jarviscog/Bertha3/CAD Files/parts/frontv2.SLDPRT

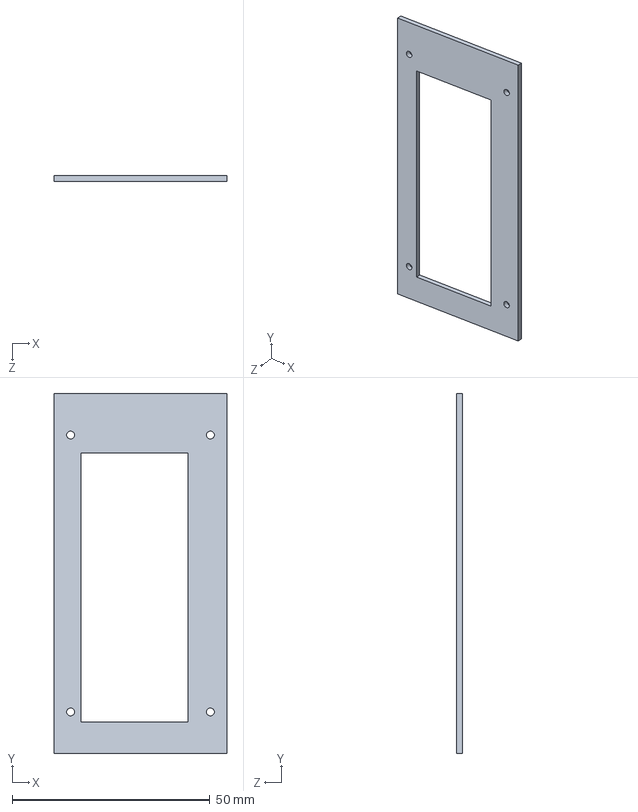
[picture p15: CAD file, 2022-08-08]
CAD Files/parts/frontv2.SLDPRT
43.7 x 91.0 x 1.50 mm
