jarviscog/Bertha3/Parts/EndCap.SLDPRT

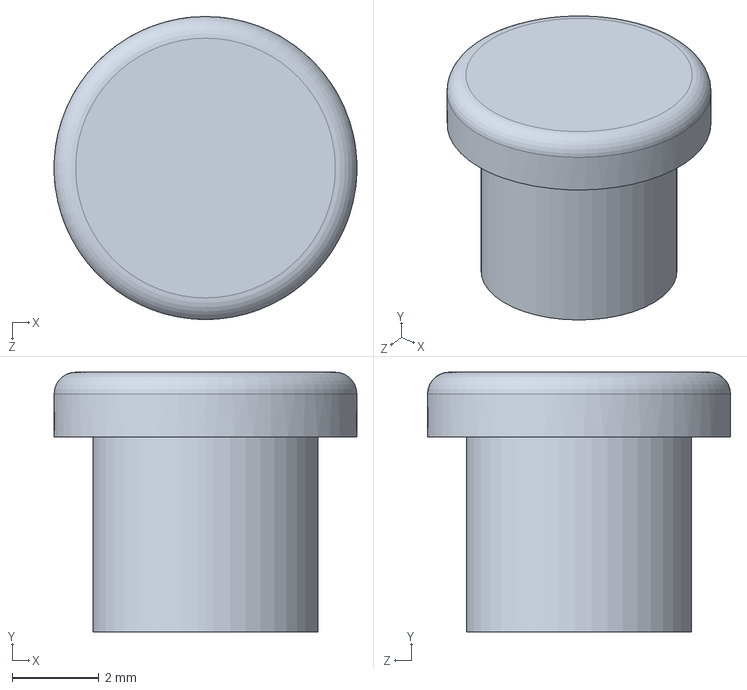
[picture p16: CAD file, 2021-05-19]
Parts/EndCap.SLDPRT
7.00 x 6.00 x 7.00 mm
