jarviscog/Bertha3/CAD Files/parts/fasteners.SLDPRT

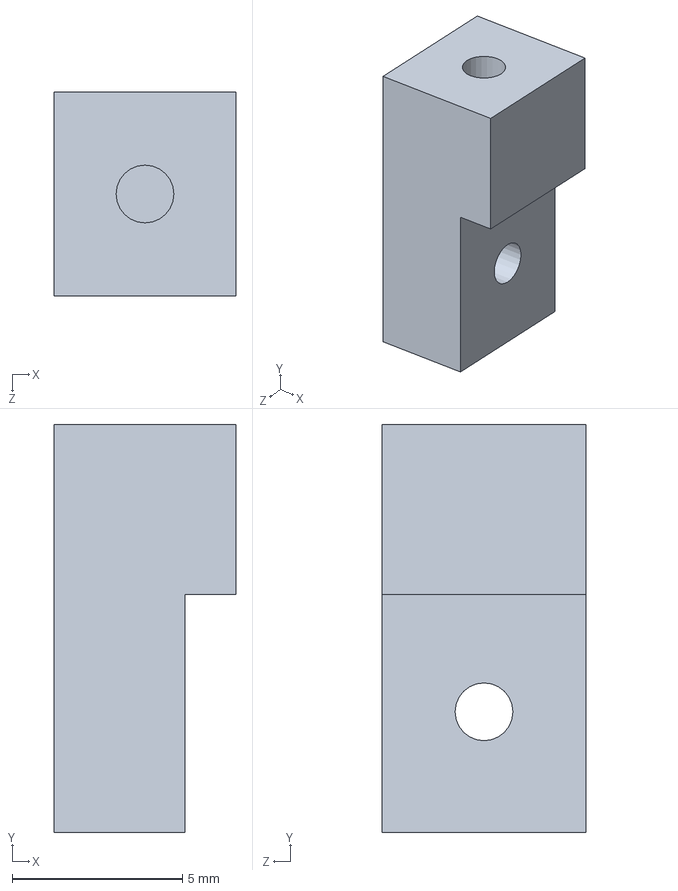
[picture p17: CAD file, 2022-08-08]
CAD Files/parts/fasteners.SLDPRT
5.35 x 12.0 x 6.00 mm
