jarviscog/Bertha3/Parts/SinisterGear.SLDPRT

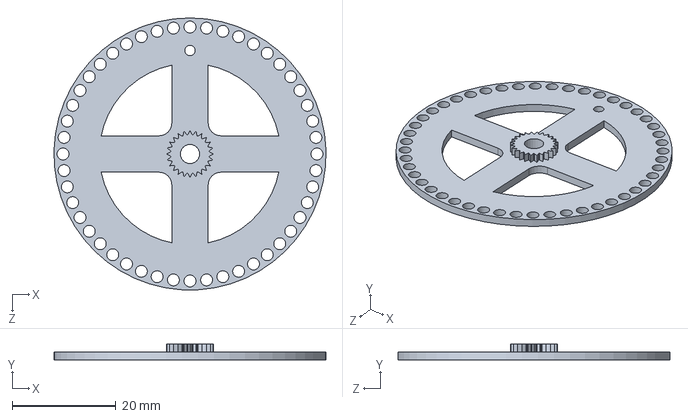
[picture p18: CAD file, 2021-05-19]
Parts/SinisterGear.SLDPRT
52.5 x 3.00 x 52.5 mm
