jarviscog/Bertha3/CAD Files/parts/Right.SLDPRT

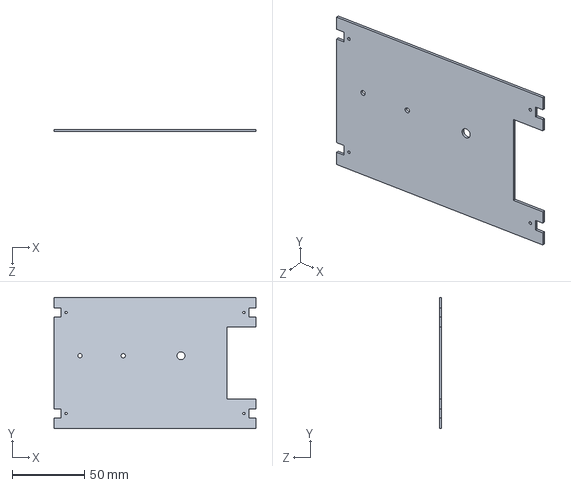
[picture p19: CAD file, 2022-08-08]
CAD Files/parts/Right.SLDPRT
140.0 x 91.0 x 1.50 mm
