jarviscog/Bertha3/Parts/Metal Rod.SLDPRT

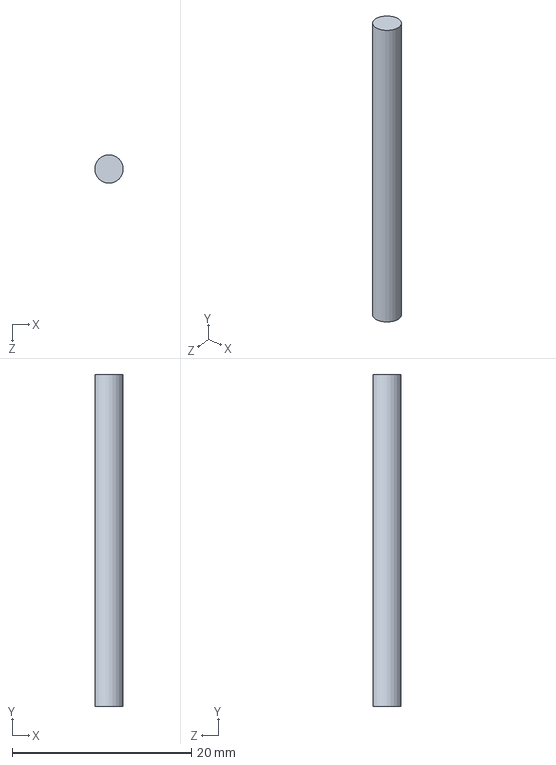
[picture p20: CAD file, 2021-05-19]
Parts/Metal Rod.SLDPRT
3.17 x 37.0 x 3.17 mm
