jarviscog/Bertha3/CAD Files/parts/backplate.SLDPRT

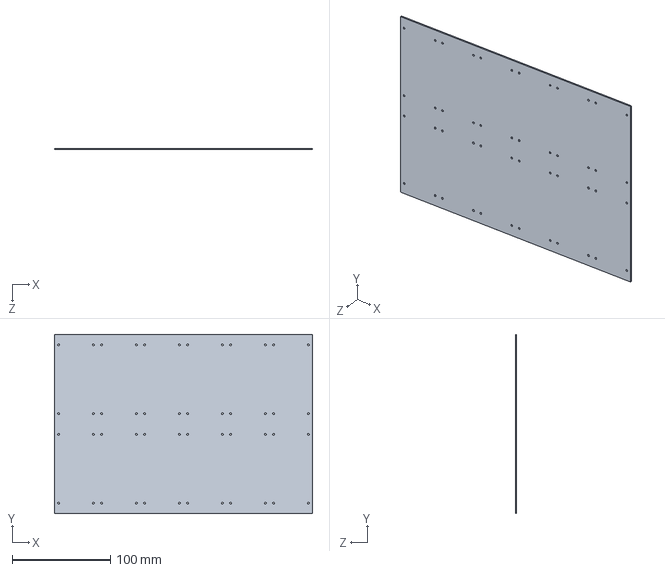
[picture p21: CAD file, 2022-08-08]
CAD Files/parts/backplate.SLDPRT
262.2 x 182.0 x 1.50 mm
