jarviscog/Bertha3/CAD Files/parts/motor_driver_pcb.SLDPRT

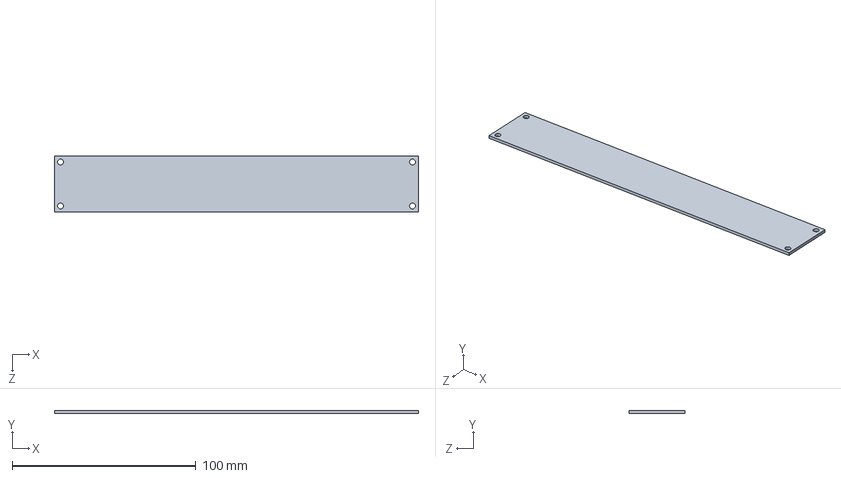
[picture p22: CAD file, 2022-08-08]
CAD Files/parts/motor_driver_pcb.SLDPRT
198.1 x 1.60 x 30.5 mm
