jarviscog/Bertha3/CAD Files/parts/BarrelSide.SLDPRT

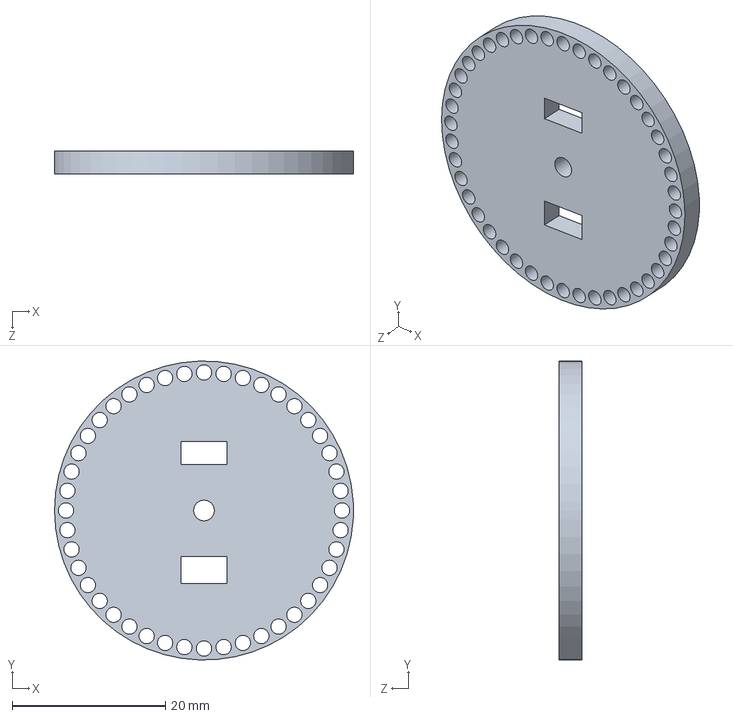
[picture p23: CAD file, 2022-08-08]
CAD Files/parts/BarrelSide.SLDPRT
39.0 x 39.0 x 3.00 mm
