jarviscog/Bertha3/CAD Files/parts/gear2.SLDPRT

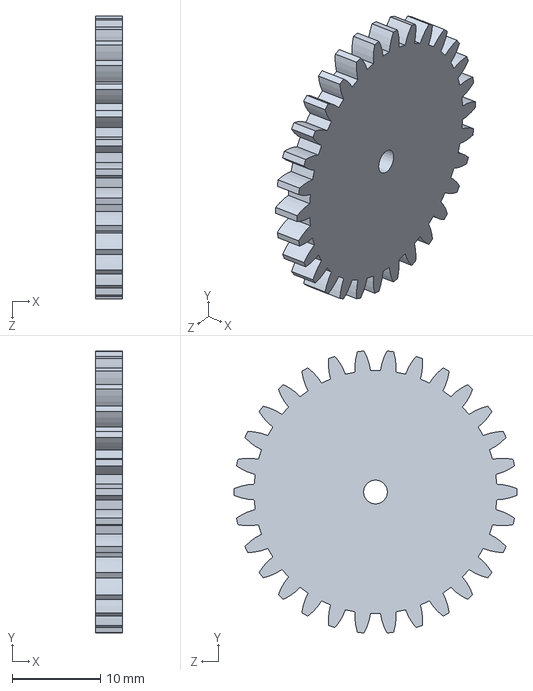
[picture p24: CAD file, 2022-07-11]
CAD Files/parts/gear2.SLDPRT
3.00 x 31.9 x 32.0 mm
