jarviscog/Bertha3/CAD Files/parts/HallSensor.SLDPRT

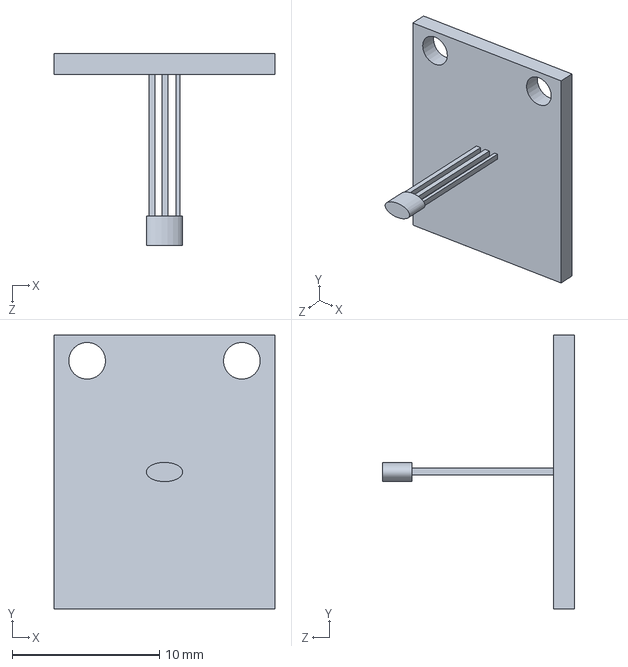
[picture p25: CAD file, 2022-07-11]
CAD Files/parts/HallSensor.SLDPRT
15.0 x 18.6 x 13.0 mm
