jarviscog/Bertha3/CAD Files/parts/Axel.SLDPRT

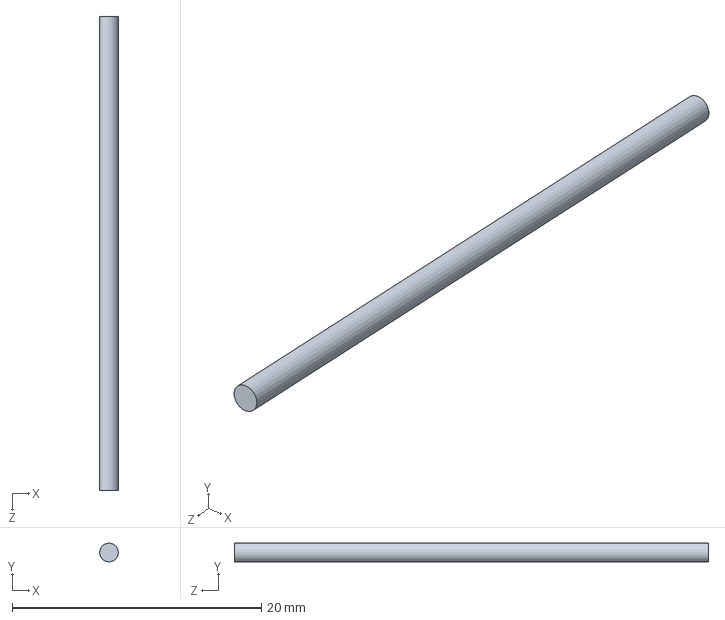
[picture p26: CAD file, 2022-07-11]
CAD Files/parts/Axel.SLDPRT
1.50 x 1.50 x 38.0 mm
