jarviscog/Bertha3/CAD Files/parts/InnerBarrelStandoff.SLDPRT

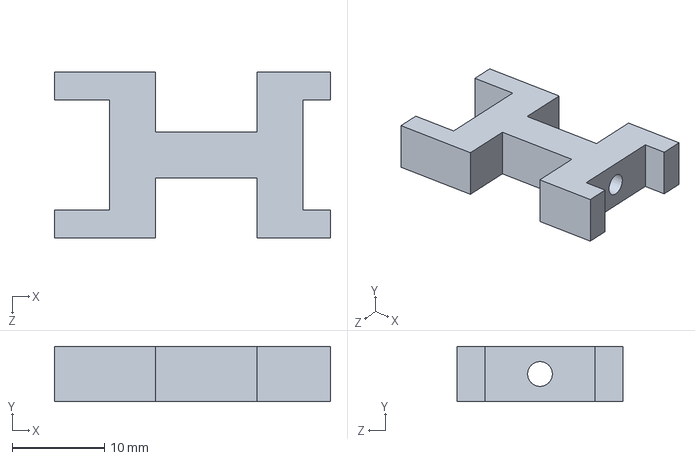
[picture p27: CAD file, 2022-07-11]
CAD Files/parts/InnerBarrelStandoff.SLDPRT
30.0 x 6.00 x 18.0 mm
