jarviscog/Bertha3/CAD Files/parts/top_sides.SLDPRT

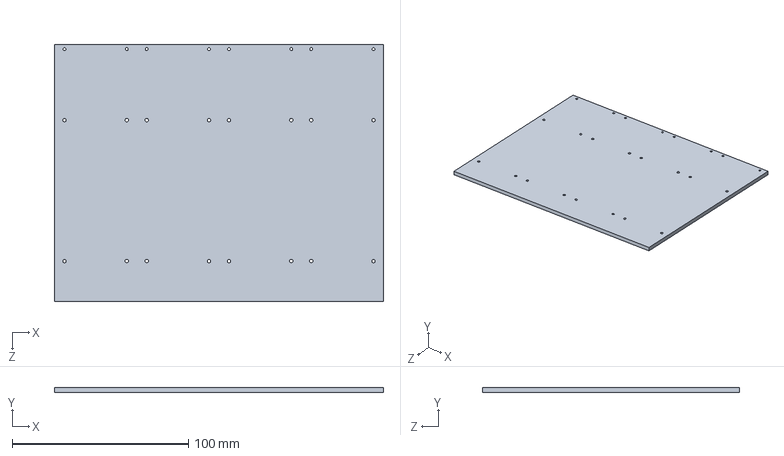
[picture p28: CAD file, 2022-07-11]
CAD Files/parts/top_sides.SLDPRT
186.8 x 3.00 x 146.0 mm
