jarviscog/Bertha3/CAD Files/parts/driving_gear.SLDPRT

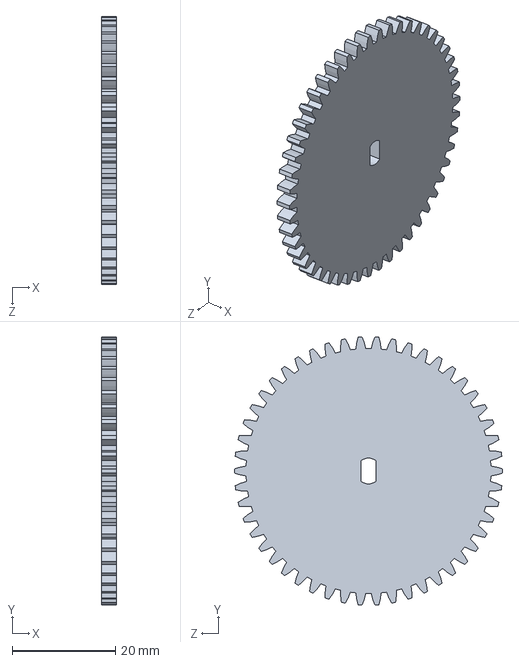
[picture p29: CAD file, 2022-07-11]
CAD Files/parts/driving_gear.SLDPRT
3.00 x 51.9 x 52.0 mm
