jarviscog/Bertha3/CAD Files/parts/Motor.SLDPRT

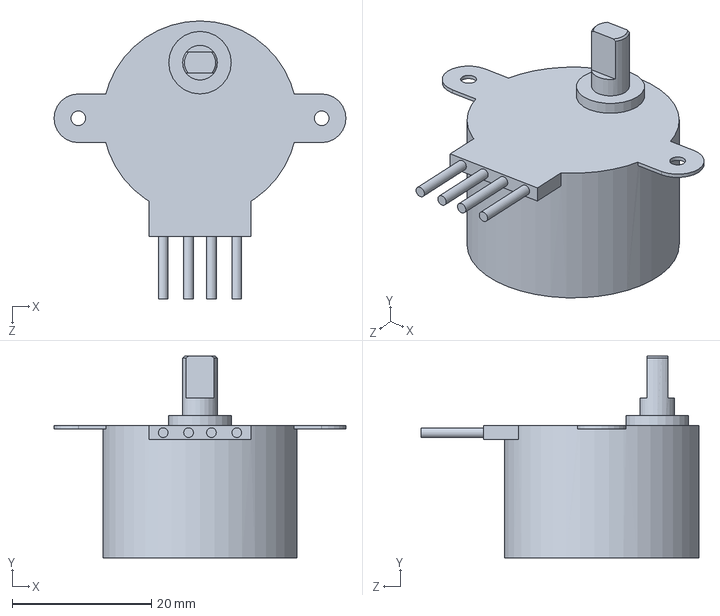
[picture p30: CAD file, 2022-07-11]
CAD Files/parts/Motor.SLDPRT
42.0 x 29.0 x 40.0 mm
