jarviscog/Bertha3/CAD Files/parts/motor_standoff.SLDPRT

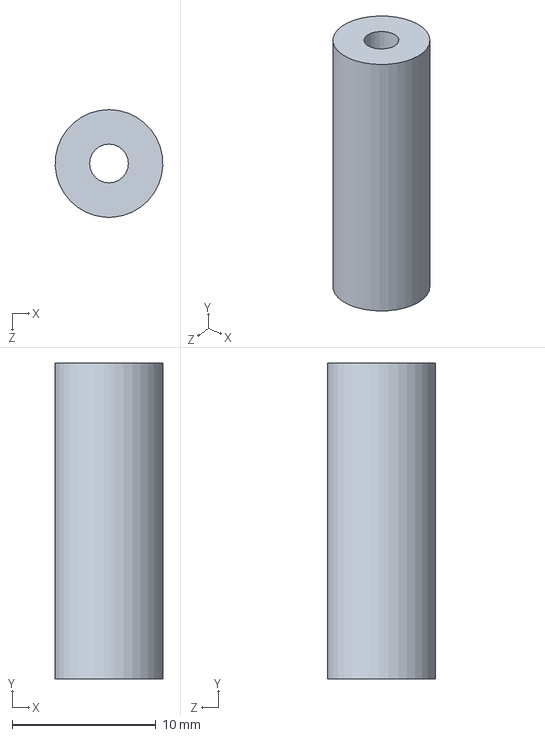
[picture p31: CAD file, 2022-07-11]
CAD Files/parts/motor_standoff.SLDPRT
7.49 x 22.0 x 7.50 mm
