jarviscog/Bertha3/CAD Files/parts/HallSensorStandoff.SLDPRT

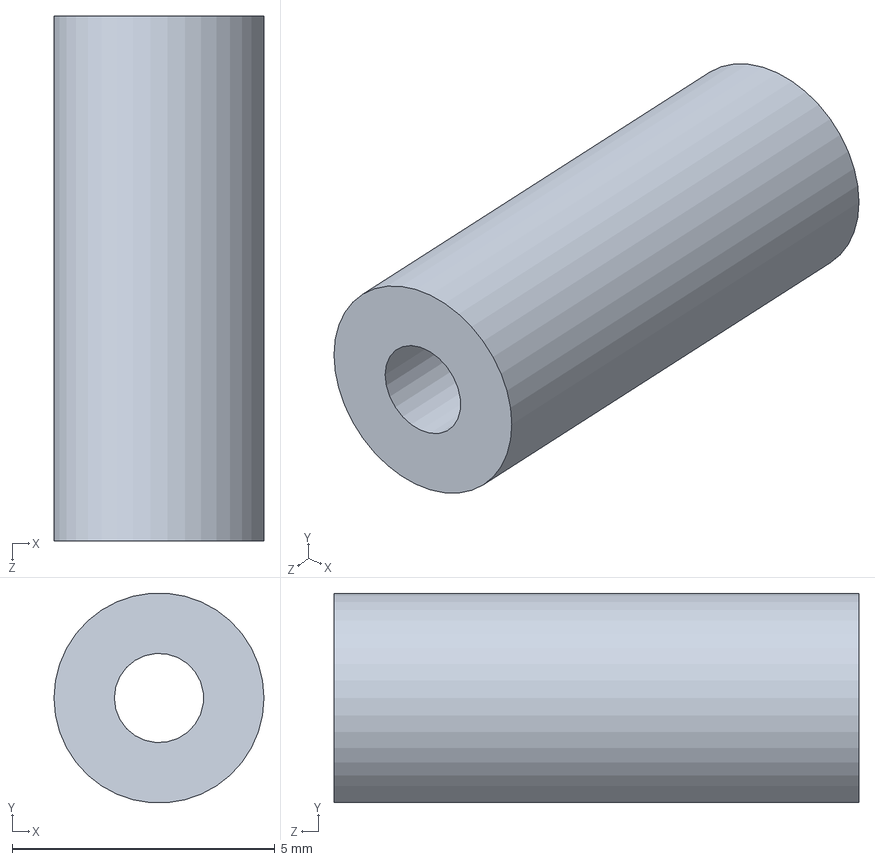
[picture p32: CAD file, 2022-07-11]
CAD Files/parts/HallSensorStandoff.SLDPRT
4.00 x 3.99 x 10.0 mm
