jarviscog/Bertha3/CAD Files/parts/flapv2.SLDPRT

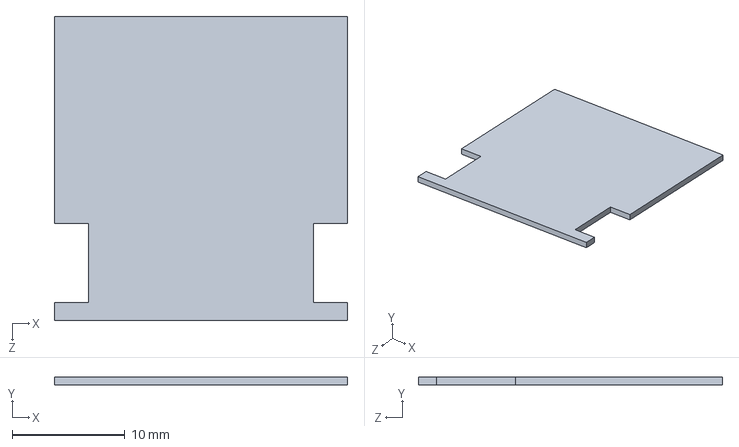
[picture p33: CAD file, 2022-07-11]
CAD Files/parts/flapv2.SLDPRT
26.0 x 0.75 x 27.0 mm
