jarviscog/Bertha3/ESP32Code/ESPCode/src/cycle_light.cpp

// #include "Freenove_WS2812_Lib_for_ESP32.h"


// #define LEDS_COUNT  8
// #define LEDS_PIN	48
// #define CHANNEL		0

// Freenove_ESP32_WS2812 strip = Freenove_ESP32_WS2812(LEDS_COUNT, LEDS_PIN, CHANNEL, TYPE_GRB);

// byte m_color[5][3] = { {255, 0, 0}, {0, 255, 0}, {0, 0, 255}, {255, 255, 255}, {0, 0, 0} };
// int delayval = 100;

// void setup() {
// 	strip.begin();
// 	strip.setBrightness(10);	
// }
// void loop() {
// 	for (int j = 0; j < 5; j++) {
// 		for (int i = 0; i < LEDS_COUNT; i++) {
// 			strip.setLedColorData(i, m_color[j][0], m_color[j][1], m_color[j][2]);
// 			strip.show();
// 			delay(delayval);
// 		}
// 		delay(500);
// 	}
// }
